shm-dmitry/supply/src/power-output-control/power_output_control.cpp

#include "power_output_control.h"

#include "Arduino.h"

#include "led.h"
#include "power_output_sense.h"

#include "config.h"

#define POWER_OUTPUT_MAX_V 50000
#define POWER_OUTPUT_MAX_I 10000

uint16_t power_output_control_I_x1000 = 0;
uint16_t power_output_control_V_x1000 = 0;

bool power_output_enabled = false;
bool power_output_control_out_enabled = false;

void power_output_control_init() {
  pinMode(PIN_POWER_OUTPUT_IC_FB, OUTPUT);
  digitalWrite(PIN_POWER_OUTPUT_IC_FB, HIGH); // disable output
  pinMode(PIN_POWER_OUTPUT_SHUTDOWN, OUTPUT);
  digitalWrite(PIN_POWER_OUTPUT_SHUTDOWN, LOW); // shutdown ON

  power_output_control_out_enabled = false;
  power_output_enabled = false;

  power_output_sense_init();
  led_init();
}

void power_output_control_on_main_loop() {
  bool allowWork = true;

  if (power_output_control_V_x1000 == 0 || power_output_control_I_x1000 == 0 || power_output_enabled == false) {
    allowWork = false;

    led_set_overloaded(false);
  } else {
    uint16_t current_I = power_output_sense_readI_x1000(true);
    uint16_t current_V = power_output_sense_readV_x1000(true);

    allowWork = current_V <= power_output_control_V_x1000 && current_I <= power_output_control_I_x1000;

    led_set_overloaded(current_I >= power_output_control_I_x1000);
  }

  if (power_output_control_out_enabled != allowWork) {
    digitalWrite(PIN_POWER_OUTPUT_IC_FB, allowWork ? LOW : HIGH);
    power_output_control_out_enabled = allowWork;
  }
}

void power_output_control_status(t_power_output_stats & status) {
  status.limit_I = power_output_control_I_x1000;
  status.limit_V = power_output_control_V_x1000;
  status.actual_I = power_output_sense_readI_x1000(false);
  status.actual_V = power_output_sense_readV_x1000(false);
  status.enabled = power_output_enabled;
}

void power_output_control_setV(uint16_t voltage_x1000) {
  power_output_control_V_x1000 = voltage_x1000;
}

void power_output_control_setI(uint16_t current_x1000) {
  power_output_control_I_x1000 = current_x1000;
}

void power_output_control_addV(uint16_t delta, bool add) {
  if (add) {
    power_output_control_V_x1000 += delta;

    if (power_output_control_V_x1000 > POWER_OUTPUT_MAX_V) {
      power_output_control_V_x1000 = POWER_OUTPUT_MAX_V;
    }
  } else {
    if (power_output_control_V_x1000 < delta) {
      power_output_control_V_x1000 = 0;
    } else {
      power_output_control_V_x1000 -= delta;
    }
  }
}

void power_output_control_addI(uint16_t delta, bool add) {
  if (add) {
    power_output_control_I_x1000 += delta;

    if (power_output_control_I_x1000 > POWER_OUTPUT_MAX_I) {
      power_output_control_I_x1000 = POWER_OUTPUT_MAX_I;
    }
  } else {
    if (power_output_control_I_x1000 < delta) {
      power_output_control_I_x1000 = 0;
    } else {
      power_output_control_I_x1000 -= delta;
    }
  }
}

void power_output_control_start(bool enable) {
  power_output_enabled = enable;

  digitalWrite(PIN_POWER_OUTPUT_SHUTDOWN, (power_output_enabled ? HIGH : LOW));
  led_set_poweroutput(enable);

  Serial.print("Change out enabled: ");
  Serial.println(power_output_enabled);
}
