shm-dmitry/supply/src/supply/display_ili9341.h

/**
This code based on projects:
- https://github.com/adafruit/Adafruit_ILI9341
- https://github.com/adafruit/Adafruit-GFX-Library
*/

#ifndef DISPLAY_ILI9341_H_
#define DISPLAY_ILI9341_H_

#include "display_spi.h"

void display_ili9341_init(uint8_t cs, uint8_t dc);

#endif /* DISPLAY_ILI9341_H_ */
