shm-dmitry/supply/src/supply/display_st7735.h

/**
This code based on projects:
- https://github.com/adafruit/Adafruit-ST7735-Library
- https://github.com/adafruit/Adafruit_ILI9341
- https://github.com/adafruit/Adafruit-GFX-Library
*/

#ifndef DISPLAY_ST7735_H_
#define DISPLAY_ST7735_H_

#include "display_spi.h"

void display_st7735_init(uint8_t cs, uint8_t dc);

#endif /* DISPLAY_ST7735_H_ */
