shm-dmitry/supply/src/supply/gui_icons.h

#ifndef GUI_ICONS_H_
#define GUI_ICONS_H_

#include "Arduino.h"

#define GUI_ICONS_USB_WIDTH 16
#define GUI_ICONS_USB_HEIGHT 16
static const uint8_t PROGMEM GUI_ICONS_USB[] = { 
   0x01, 0x80, 0xf3, 0xc0, 0x93, 0xcf, 0x91, 0x89, 0xf1, 0x89, 0x61, 0x9f,
   0x31, 0xb8, 0x3d, 0xf0, 0x0f, 0xc0, 0x03, 0x80, 0x01, 0x80, 0x03, 0xc0,
   0x06, 0x60, 0x06, 0x60, 0x03, 0xc0, 0x01, 0x80};




#endif /* GUI_ICONS_H_ */
